dhansel/VersaTerm/hardware/pictures/enc_diag2.jpg

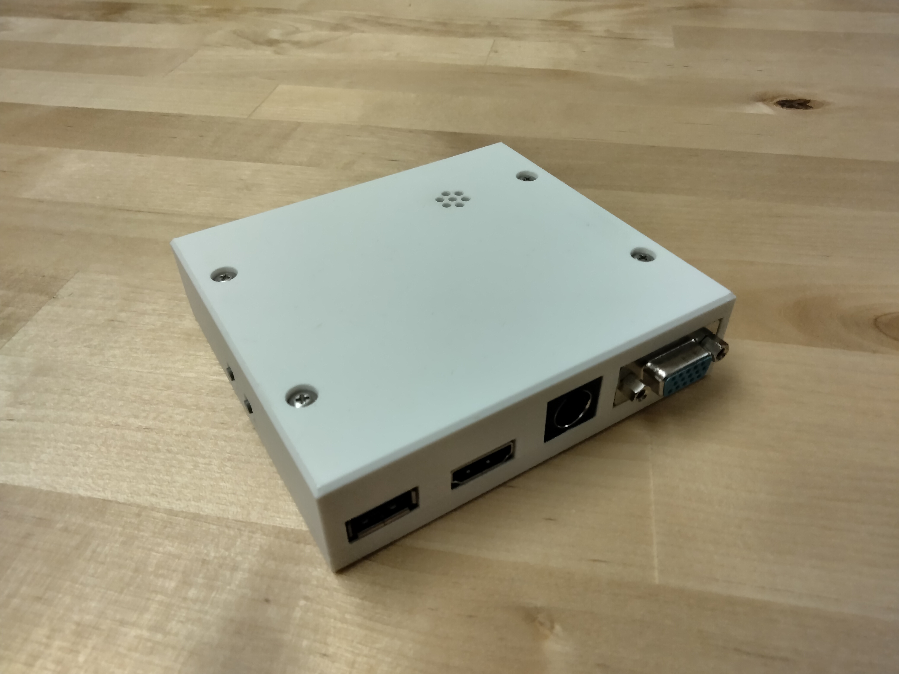
hardware/pictures/enc_diag2.jpg
