dhansel/VersaTerm/software/src/keyboard_usb.c

// -----------------------------------------------------------------------------
// VersaTerm - A versatile serial terminal
// Copyright (C) 2022 David Hansel
//
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
#include "keyboard.h"
#include "keyboard_usb.h"
#include "config.h"
#include "pico/time.h"
#include "tusb.h"
#include "config.h"
#include "keyboard.h"
#include <ctype.h>

//#define DEBUG

#ifdef DEBUG
#include "terminal.h"
#include <stdarg.h>
static void print(const char *format, ...)
{
  char buffer[101];
  va_list argptr;
  va_start(argptr, format);
  vsnprintf(buffer, 100, format, argptr);
  terminal_receive_string(buffer);
  va_end(argptr);
}
#else
#define print(...)
#endif


//--------------------------------------------------------------------+
// Keyboard functions
//--------------------------------------------------------------------+

static uint8_t keyboard_repeat_key = 0;
static absolute_time_t keyboard_repeat_timeout = 0;
static uint8_t s_leds, keyboard_dev_addr = 0xFF, keyboard_instance = 0xFF;


void keyboard_usb_set_led_status(uint8_t leds)
{
  if( keyboard_dev_addr!=0xFF && keyboard_instance!=0xFF )
    {
      s_leds = leds;
      tuh_hid_set_report(keyboard_dev_addr, keyboard_instance, 0, HID_REPORT_TYPE_OUTPUT, &s_leds, sizeof(s_leds));
    }
}


// look up new key in previous keys
static inline bool find_key_in_report(const hid_keyboard_report_t *report, uint8_t keycode)
{
  for(uint8_t i=0; i<6; i++)
    if (report->keycode[i] == keycode)  
      return true;

  return false;
}


static void process_kbd_report(uint8_t dev_addr, uint8_t instance, hid_keyboard_report_t const *report)
{
  static hid_keyboard_report_t prev_report = { 0, 0, {0} }; // previous report to check key released

  // transform modifier changes back into keypresses - the HID keyboard boot protocol keeps 
  // track of modifier keys but we need the raw keypresses (for mapping modifier keys)
  if( prev_report.modifier != report->modifier )
    {
      uint8_t mod1 = prev_report.modifier, mod2 = report->modifier;
      if( (mod1 & KEYBOARD_MODIFIER_LEFTSHIFT)!=(mod2 & KEYBOARD_MODIFIER_LEFTSHIFT) )
        keyboard_key_change(HID_KEY_SHIFT_LEFT, (mod2 & KEYBOARD_MODIFIER_LEFTSHIFT)!=0);
      if( (mod1 & KEYBOARD_MODIFIER_RIGHTSHIFT)!=(mod2 & KEYBOARD_MODIFIER_RIGHTSHIFT) )
        keyboard_key_change(HID_KEY_SHIFT_RIGHT, (mod2 & KEYBOARD_MODIFIER_RIGHTSHIFT)!=0);
      if( (mod1 & KEYBOARD_MODIFIER_LEFTCTRL)!=(mod2 & KEYBOARD_MODIFIER_LEFTCTRL) )
        keyboard_key_change(HID_KEY_CONTROL_LEFT, (mod2 & KEYBOARD_MODIFIER_LEFTCTRL)!=0);
      if( (mod1 & KEYBOARD_MODIFIER_RIGHTCTRL)!=(mod2 & KEYBOARD_MODIFIER_RIGHTCTRL) )
        keyboard_key_change(HID_KEY_CONTROL_RIGHT, (mod2 & KEYBOARD_MODIFIER_RIGHTCTRL)!=0);
      if( (mod1 & KEYBOARD_MODIFIER_LEFTALT)!=(mod2 & KEYBOARD_MODIFIER_LEFTALT) )
        keyboard_key_change(HID_KEY_ALT_LEFT, (mod2 & KEYBOARD_MODIFIER_LEFTALT)!=0);
      if( (mod1 & KEYBOARD_MODIFIER_RIGHTALT)!=(mod2 & KEYBOARD_MODIFIER_RIGHTALT) )
        keyboard_key_change(HID_KEY_ALT_RIGHT, (mod2 & KEYBOARD_MODIFIER_RIGHTALT)!=0);
      if( (mod1 & KEYBOARD_MODIFIER_LEFTGUI)!=(mod2 & KEYBOARD_MODIFIER_LEFTGUI) )
        keyboard_key_change(HID_KEY_GUI_LEFT, (mod2 & KEYBOARD_MODIFIER_LEFTGUI)!=0);
      if( (mod1 & KEYBOARD_MODIFIER_RIGHTGUI)!=(mod2 & KEYBOARD_MODIFIER_RIGHTGUI) )
        keyboard_key_change(HID_KEY_GUI_RIGHT, (mod2 & KEYBOARD_MODIFIER_RIGHTGUI)!=0);
    }

  for(uint8_t i=0; i<6; i++)
    if( report->keycode[i]!=HID_KEY_NONE && !find_key_in_report(&prev_report, report->keycode[i]) )
      {
        // key was newly pressed
        keyboard_key_change(report->keycode[i], true);
        keyboard_repeat_key = report->keycode[i];
        keyboard_repeat_timeout = make_timeout_time_ms(config_get_keyboard_repeat_delay_ms());
      }
  
  for(uint8_t i=0; i<6; i++)
    if( prev_report.keycode[i]!=HID_KEY_NONE && !find_key_in_report(report, prev_report.keycode[i]) )
      {
        // key was released
        keyboard_key_change(prev_report.keycode[i], false);
        if( prev_report.keycode[i] == keyboard_repeat_key )
          keyboard_repeat_key = HID_KEY_NONE;
      }

  prev_report = *report;
}


void keyboard_usb_task()
{
  if( keyboard_repeat_key!=HID_KEY_NONE && get_absolute_time() >= keyboard_repeat_timeout )
    {
      keyboard_key_change(keyboard_repeat_key, true);
      keyboard_repeat_timeout = make_timeout_time_ms(1000000/config_get_keyboard_repeat_rate_mHz());
    }
}


void keyboard_usb_apply_settings()
{
}


void keyboard_usb_init()
{
}



//--------------------------------------------------------------------+
// TinyUSB Callbacks
//--------------------------------------------------------------------+


// Invoked when device with hid interface is mounted
// We only use the boot protocol and therefore can ignore the report descriptor
void tuh_hid_mount_cb(uint8_t dev_addr, uint8_t instance, uint8_t const* desc_report, uint16_t desc_len)
{
  uint8_t const itf_protocol = tuh_hid_interface_protocol(dev_addr, instance);

  if( itf_protocol == HID_ITF_PROTOCOL_KEYBOARD )
    {
      keyboard_dev_addr = dev_addr;
      keyboard_instance = instance;
      keyboard_usb_set_led_status(keyboard_get_led_status());
      keyboard_repeat_key = HID_KEY_NONE;
    }

  // request to receive report
  tuh_hid_receive_report(dev_addr, instance);
}


void tuh_hid_umount_cb(uint8_t dev_addr, uint8_t instance)
{
  if( dev_addr==keyboard_dev_addr && instance==keyboard_instance )
    {
      keyboard_dev_addr = 0xFF;
      keyboard_instance = 0xFF;
    }
}


// Invoked when received report from device via interrupt endpoint
void tuh_hid_report_received_cb(uint8_t dev_addr, uint8_t instance, uint8_t const* report, uint16_t len)
{
  uint8_t const itf_protocol = tuh_hid_interface_protocol(dev_addr, instance);

  if( itf_protocol==HID_ITF_PROTOCOL_KEYBOARD )
    process_kbd_report(dev_addr, instance, (hid_keyboard_report_t const*) report);

  // continue to request to receive report
  tuh_hid_receive_report(dev_addr, instance);
}
